koldfrontier/dgx-spark-ops/design/cooling-cage/images/front.png

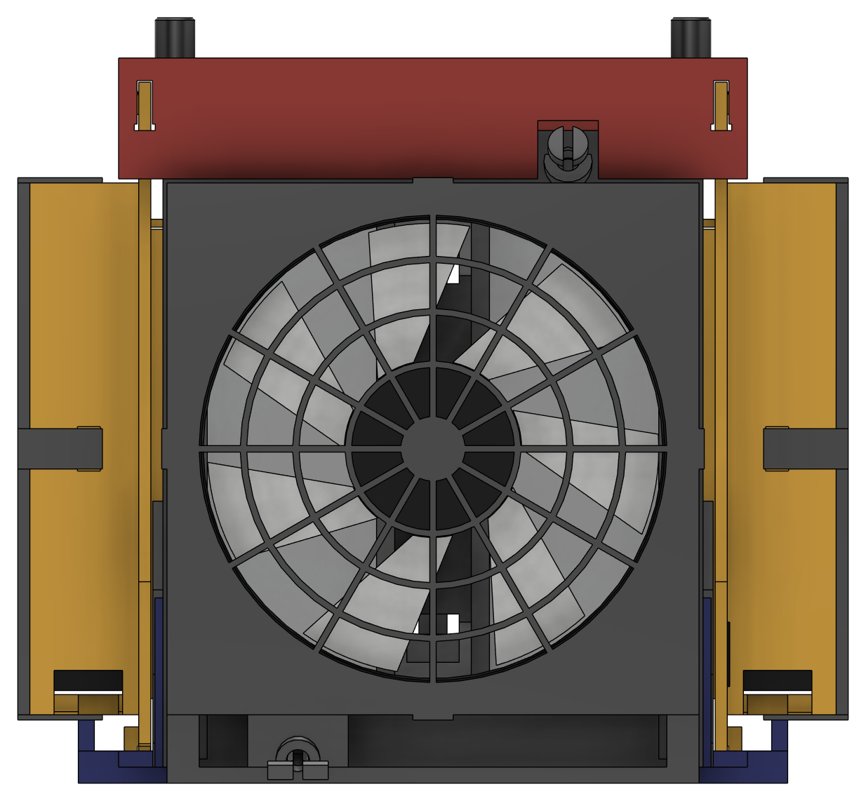
design/cooling-cage/images/front.png
