koldfrontier/dgx-spark-ops/design/cooling-cage/images/gland_detail.png

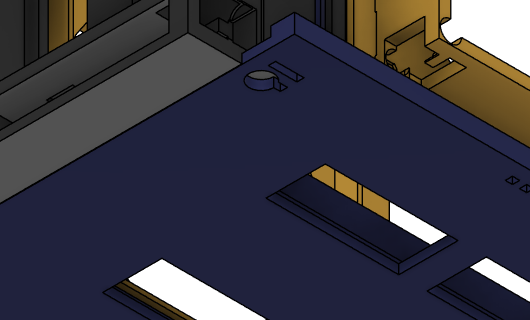
design/cooling-cage/images/gland_detail.png
