koldfrontier/dgx-spark-ops/design/cooling-cage/images/rear.png

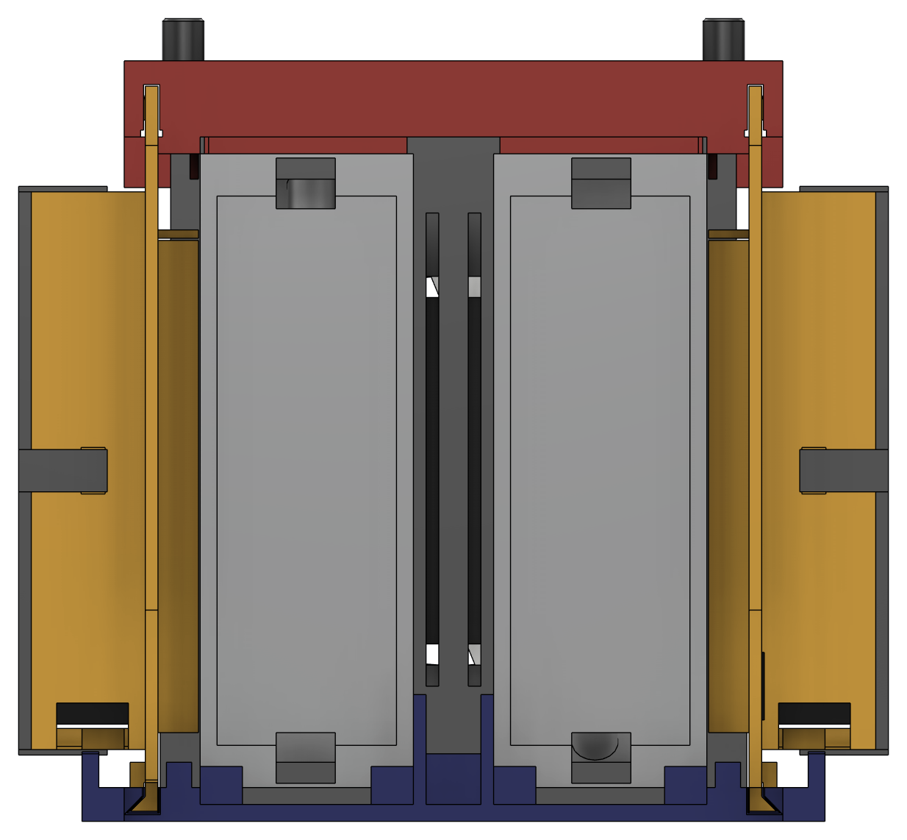
design/cooling-cage/images/rear.png
