koldfrontier/dgx-spark-ops/design/cooling-cage/images/s3_plenum.png

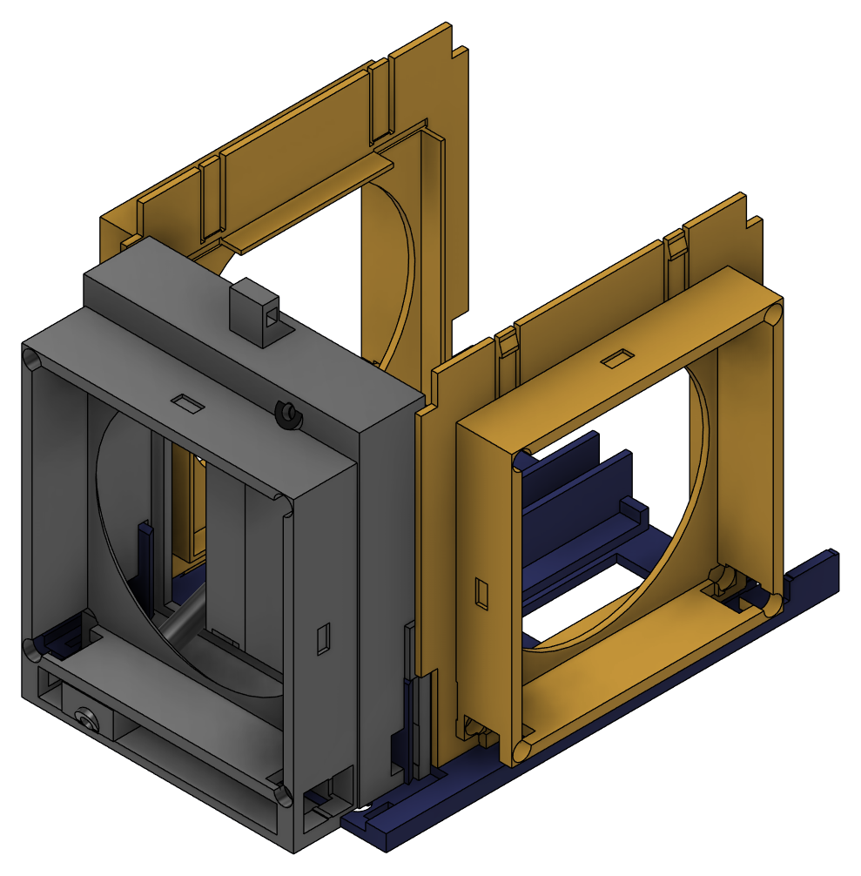
design/cooling-cage/images/s3_plenum.png
