koldfrontier/dgx-spark-ops/design/cooling-cage/images/s4_sparks.png

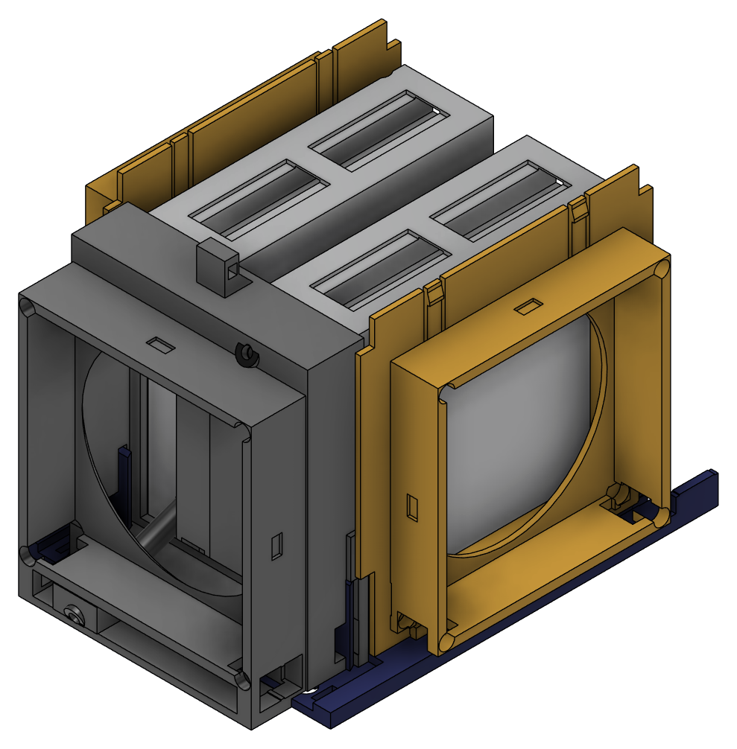
design/cooling-cage/images/s4_sparks.png
