koldfrontier/dgx-spark-ops/design/cooling-cage/images/s7_brace.png

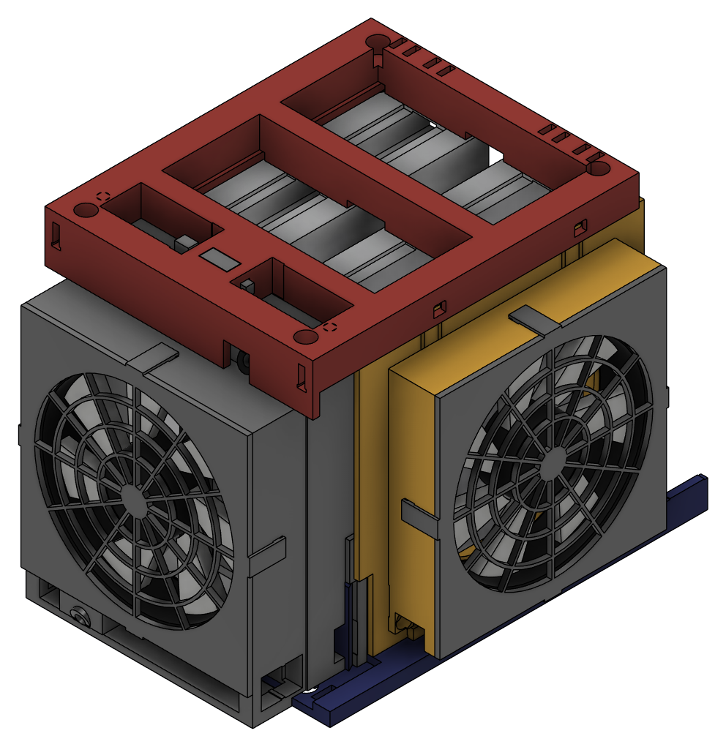
design/cooling-cage/images/s7_brace.png
